dowster/e28-cluster/code/main/fuel_gauge.c

#include "include/fuel_gauge.h"

static dac_channel_t fuel_gauge_channel = -1;
static gpio_num_t low_fuel_indicator_pin = -1;

void setup_fuel_gauge(dac_channel_t gauge, gpio_num_t low_fuel_indicator) 
{
    if(gauge != -1)
    {
        esp_err_t error = dac_output_enable(gauge);
        if(error == ESP_OK)
        {
            fuel_gauge_channel = gauge;
        }
    }

    if(low_fuel_indicator != -1 && (
            low_fuel_indicator < GPIO_NUM_34 || // pins 34 - 39 on esp32 are
            low_fuel_indicator > GPIO_NUM_39    // input only
        ))
    {
        gpio_config_t config = {
            .pin_bit_mask = low_fuel_indicator,
            .mode = GPIO_MODE_OUTPUT,
            .pull_up_en = GPIO_PULLUP_DISABLE,
            .pull_down_en = GPIO_PULLDOWN_ENABLE,
            .intr_type = GPIO_INTR_DISABLE
        };
        esp_err_t error = gpio_config(&config);
        if(error == ESP_OK) 
        {
            low_fuel_indicator_pin = low_fuel_indicator;
        }

    }
}

void write_to_fuel_gauge(int percent_full)
{
    if(fuel_gauge_channel == -1)
    {
        ESP_LOGE("write_to_fuel_gauge", "Fuel gauge not yet initialized, please call setup_fuel_gauge first.");
    }
    else
    {
        int voltage = 70 + ((percent_full * 80) / 100);
        voltage &= 255;
        ESP_LOGI("FUEL VOLTAGE", "[V: %d, %% Full: %d]", voltage, percent_full);
        dac_output_voltage(fuel_gauge_channel, voltage);
    }
}

/**
 * Turns the low fuel indicator light on if it's hooked up.
 */
void enable_low_fuel_indicator()
{
    if(low_fuel_indicator_pin == -1)
    {
        ESP_LOGE("enable_low_fuel_indicator", "low fuel indicator not yet initialized, please call setup_fuel_gauge first.");
    }
    else
    {
        gpio_set_level(low_fuel_indicator_pin, 1);
    }
}

void disable_low_fuel_indicator()
{
    if(low_fuel_indicator_pin == -1)
    {
        ESP_LOGE("enable_low_fuel_indicator", "low fuel indicator not yet initialized, please call setup_fuel_gauge first.");
    }
    else
    {
        gpio_set_level(low_fuel_indicator_pin, 0);
    }
}
